keotl/pedal-master/pcb-rev2/pedal-controller/pedal-controller.sch

## KiCad design pcb-rev2/pedal-controller/pedal-controller.sch (2019-11-30)

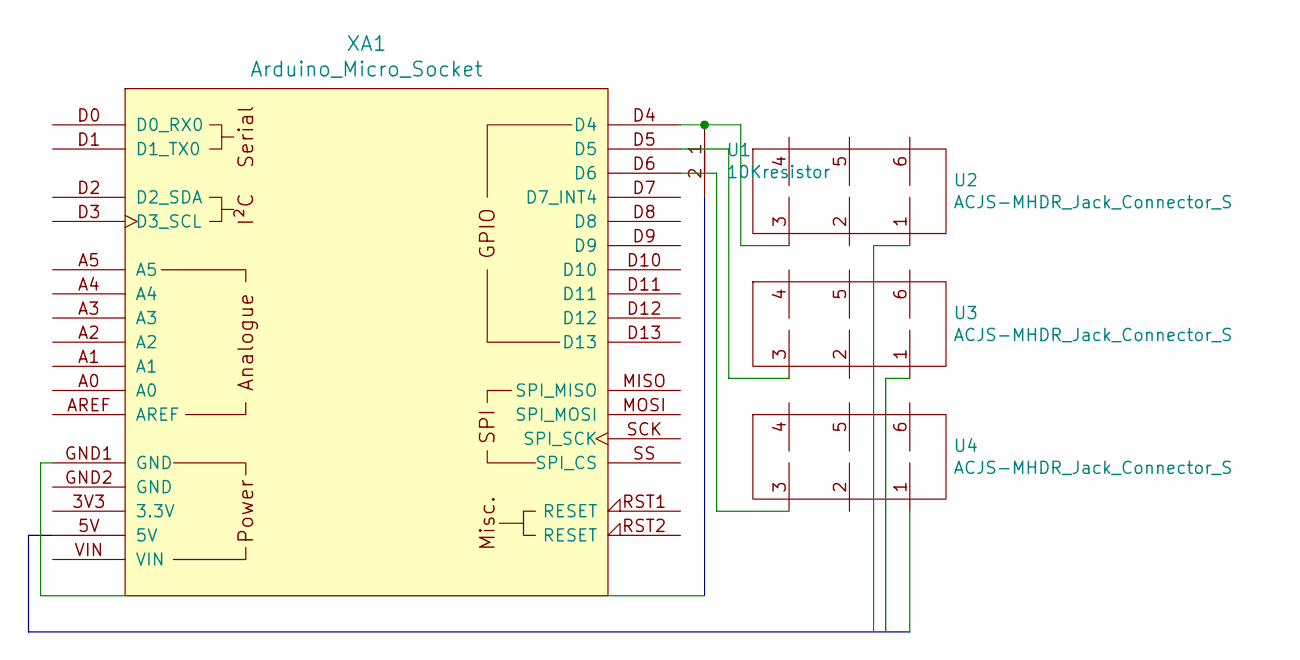
[picture p8: schematic pedal-controller.sch]

Parts:
U1: 10Kresistor
U2, U3, U4: ACJS-MHDR_Jack_Connector_S
XA1: Arduino_Micro_Socket

Connections:
unnamed: U1.1, U2.3, XA1.D4
unnamed: U3.3, XA1.D5
unnamed: U4.3, XA1.D6
